Mr-Hansen-Orewa/Nano-Atmega168-Development-Board/Software/LDR/LDR.ino

//ID 12345

const byte LDRPIN = A0;
const byte LEDPIN = 13;
int scaryDark = 600;

void setup() {
  pinMode(LDRPIN, INPUT);
  pinMode(LEDPIN, OUTPUT);

  Serial.begin(9600);
}

void loop() {
  int LDRValue = analogRead(LDRPIN);

  if (LDRValue >= scaryDark) {
    digitalWrite(LEDPIN, HIGH);
    Serial.print("Night light is on, LDR value is ");
    Serial.println(LDRValue);
  } else {
    digitalWrite(LEDPIN, LOW);
    Serial.print("Night light is off, LDR value is ");
    Serial.println(LDRValue);
  }
  delay(250);
}
